OLIMEX/ESP32-C6-EVB/HARDWARE/Hardware-revision-A/3d/Cap_PTH_6_3x11x2_5mm.step

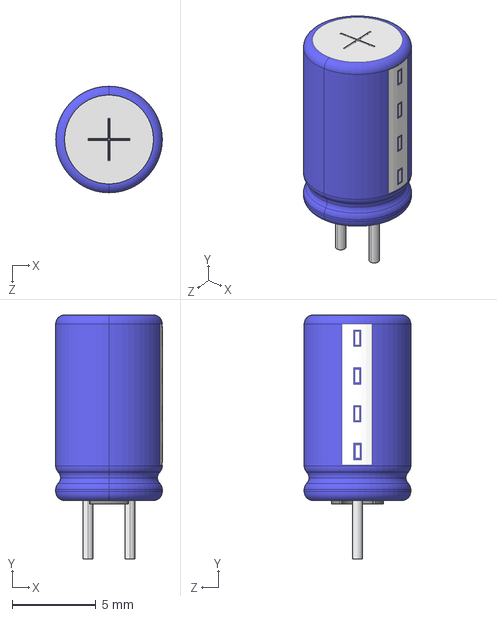
[picture p16: CAD file, 2023-07-04]
HARDWARE/Hardware-revision-A/3d/Cap_PTH_6_3x11x2_5mm.step
6.35 x 14.5 x 6.35 mm
