OLIMEX/ESP32-C6-EVB/HARDWARE/Hardware-revision-A/3d/klema-5mm-3pin.step

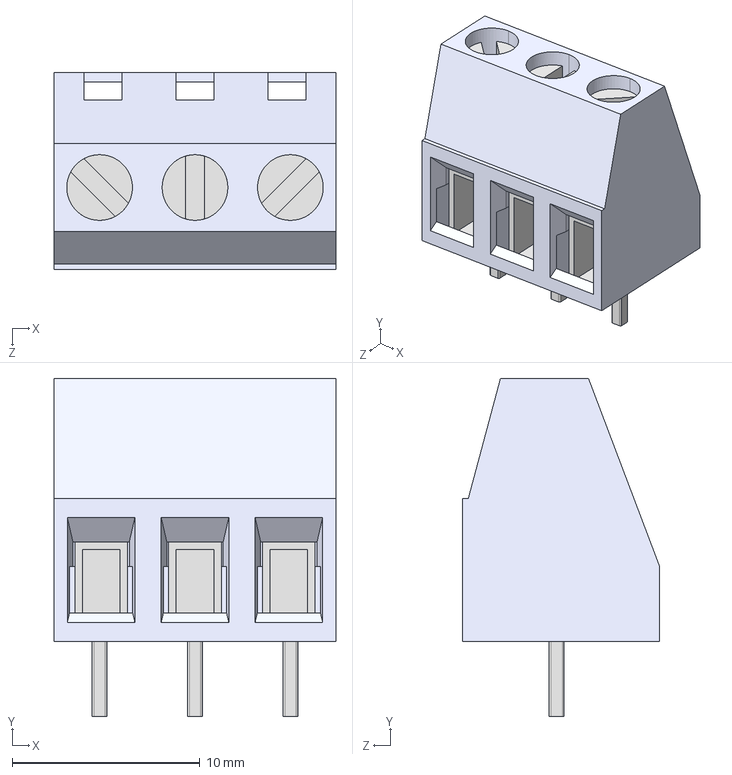
[picture p17: CAD file, 2023-07-04]
HARDWARE/Hardware-revision-A/3d/klema-5mm-3pin.step
15.0 x 18.0 x 10.5 mm
