OLIMEX/ESP32-C6-EVB/HARDWARE/Hardware-revision-A/3d/ESP32-WROOM-32D-56544.STEP

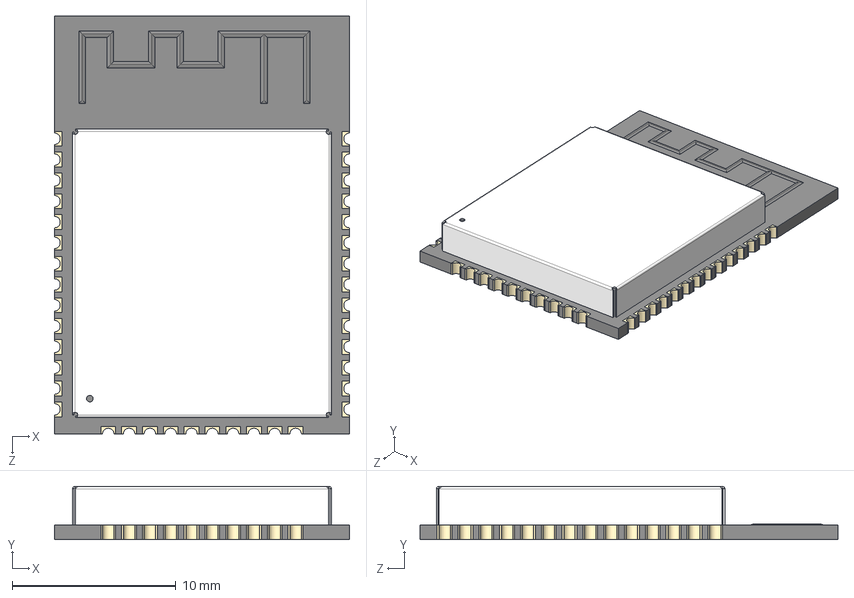
[picture p18: CAD file, 2023-07-04]
HARDWARE/Hardware-revision-A/3d/ESP32-WROOM-32D-56544.STEP
18.0 x 3.25 x 25.5 mm
