OLIMEX/ESP32-C6-EVB/HARDWARE/Hardware-revision-A/3d/DO-214AC_SMA.step

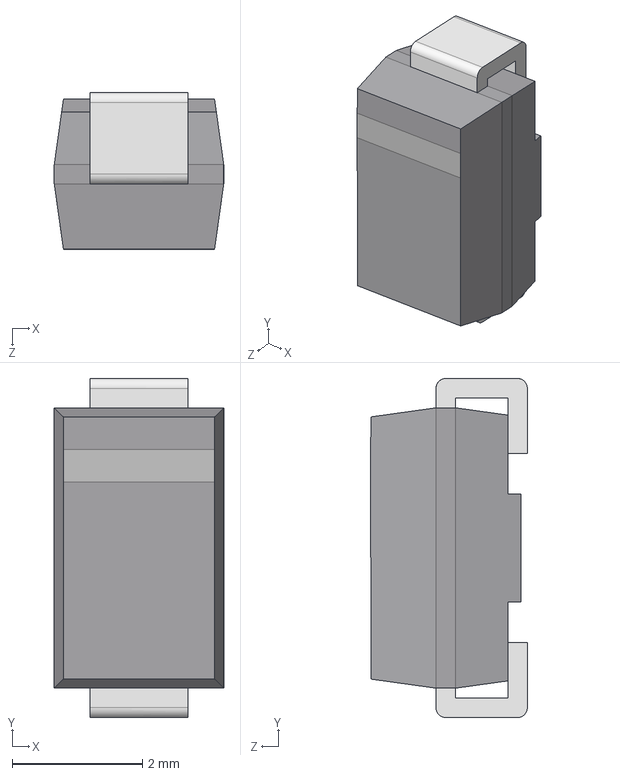
[picture p19: CAD file, 2023-07-04]
HARDWARE/Hardware-revision-A/3d/DO-214AC_SMA.step
2.60 x 5.20 x 2.40 mm
