OLIMEX/ESP32-C6-EVB/HARDWARE/Hardware-revision-A/3d/SOD123.step

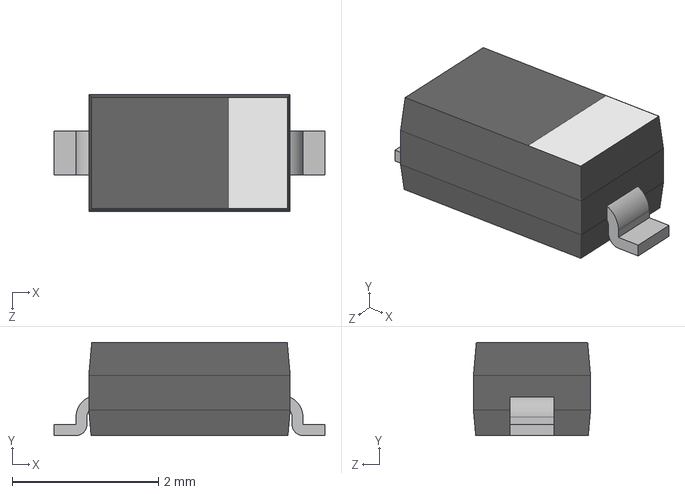
[picture p20: CAD file, 2023-07-04]
HARDWARE/Hardware-revision-A/3d/SOD123.step
3.70 x 1.27 x 1.60 mm
