OLIMEX/ESP32-C6-EVB/HARDWARE/Hardware-revision-A/3d/L_AX97-103R3.step

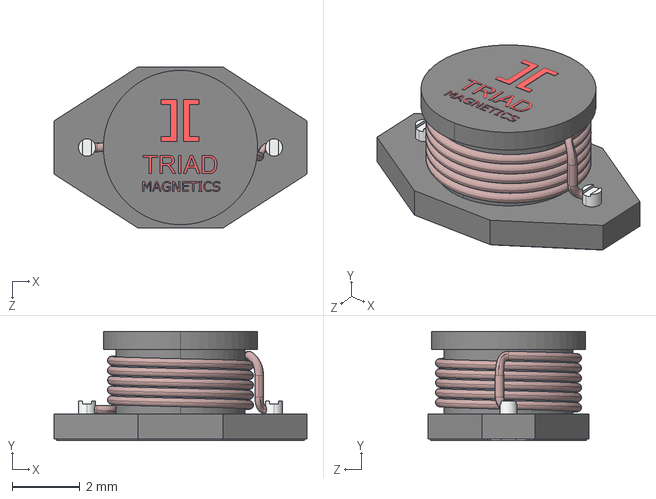
[picture p21: CAD file, 2023-07-04]
HARDWARE/Hardware-revision-A/3d/L_AX97-103R3.step
7.49 x 3.24 x 4.78 mm
